go4retro/CC40_ROMCart/pcb/CC40 ROM Cart PCB.png

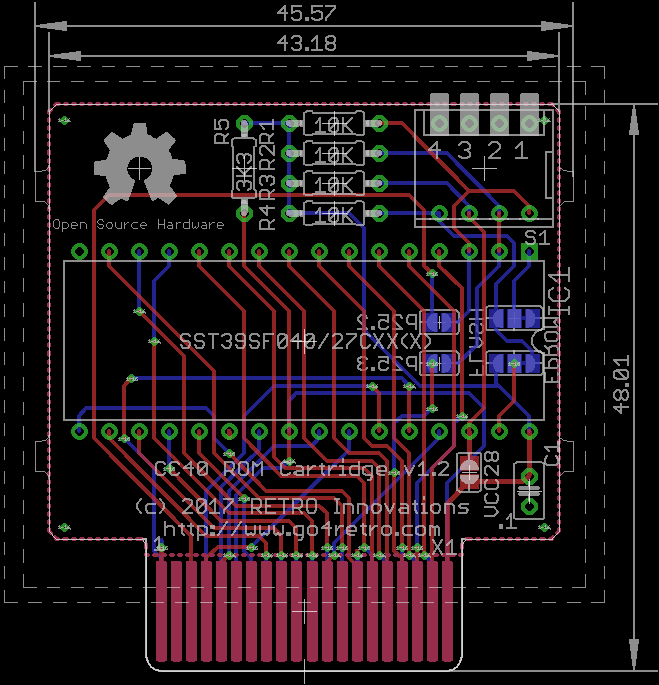
pcb/CC40 ROM Cart PCB.png
