go4retro/CC40_ROMCart/ref/ea-mp back.jpg

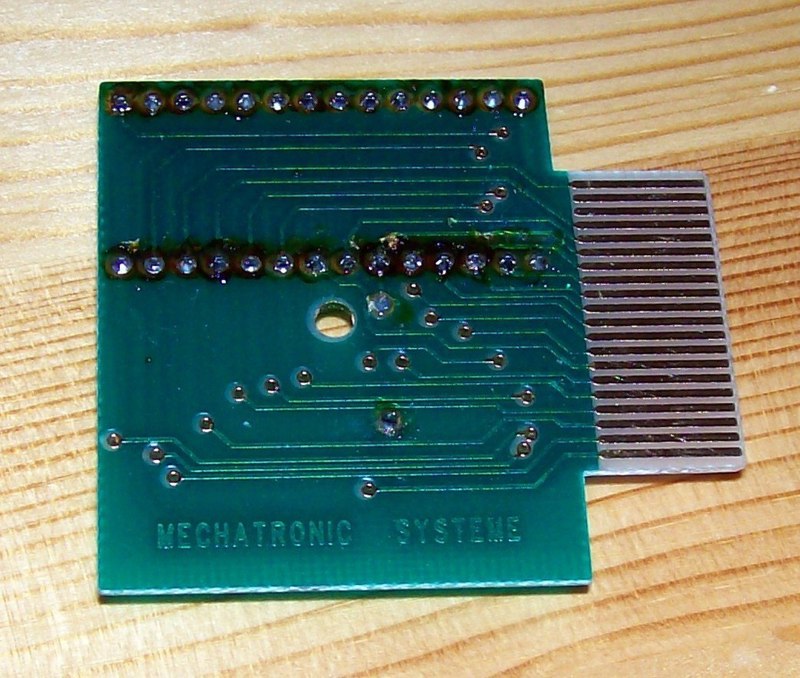
ref/ea-mp back.jpg
