go4retro/CC40_ROMCart/ref/ea-mp front.jpg

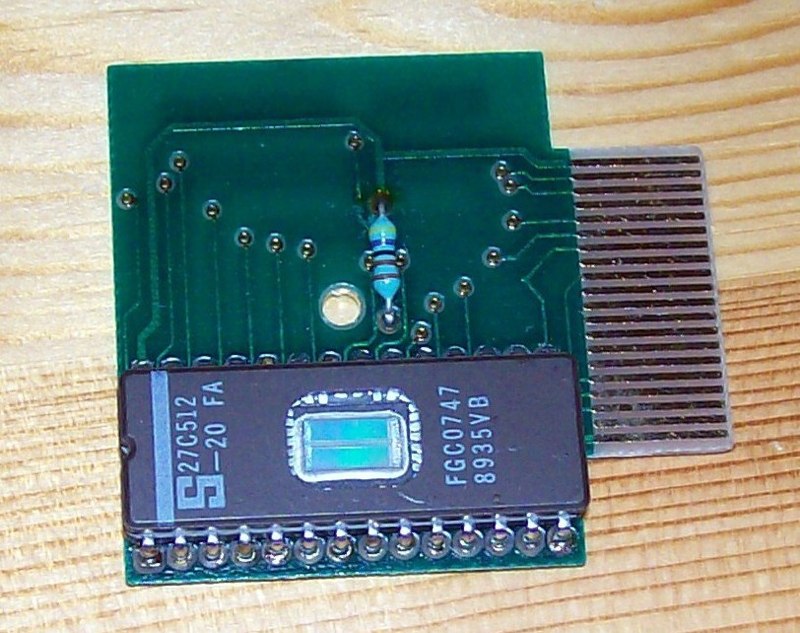
ref/ea-mp front.jpg
