go4retro/CC40_ROMCart/ref/ea-mp front_cropped.jpg

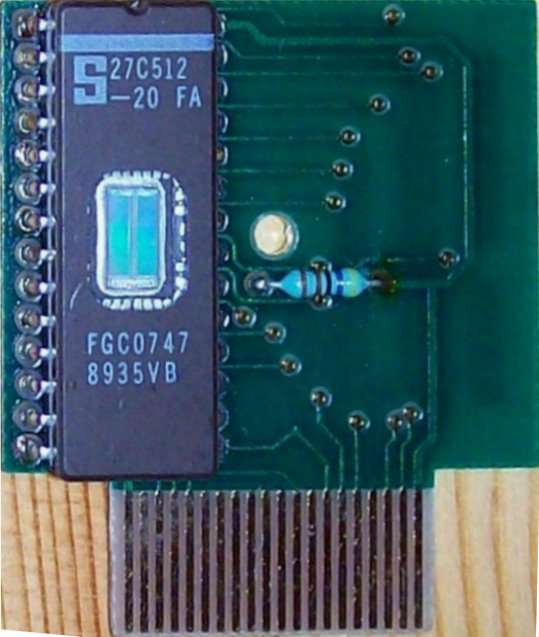
ref/ea-mp front_cropped.jpg
