go4retro/CC40_ROMCart/ref/post-48993-0-29297000-1509300581.jpg

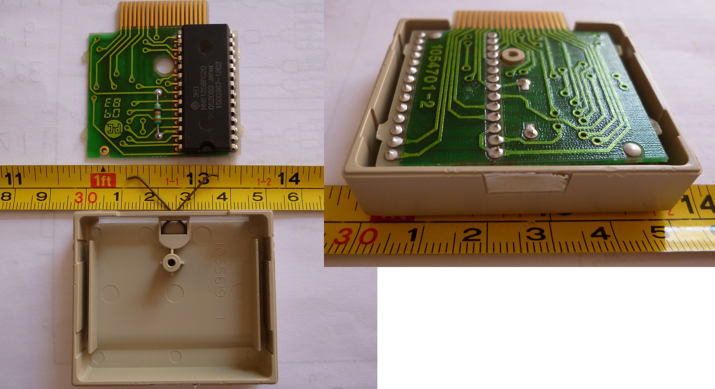
ref/post-48993-0-29297000-1509300581.jpg
