go4retro/CC40_ROMCart/ref/post-48993-0-83907700-1509300608.jpg

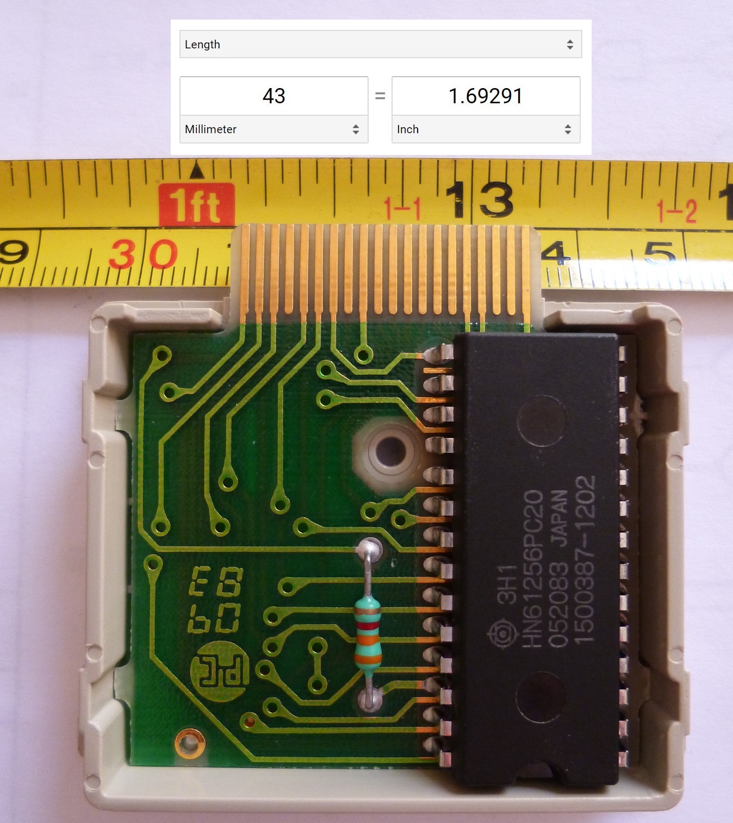
ref/post-48993-0-83907700-1509300608.jpg
